Sadrita404/Split-Keyboard/IMAGES/6.png

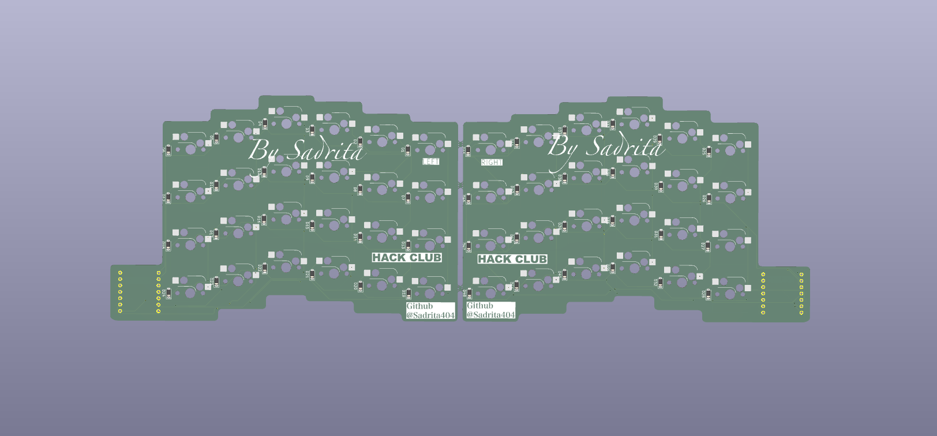
IMAGES/6.png
