Sadrita404/Split-Keyboard/IMAGES/1.png

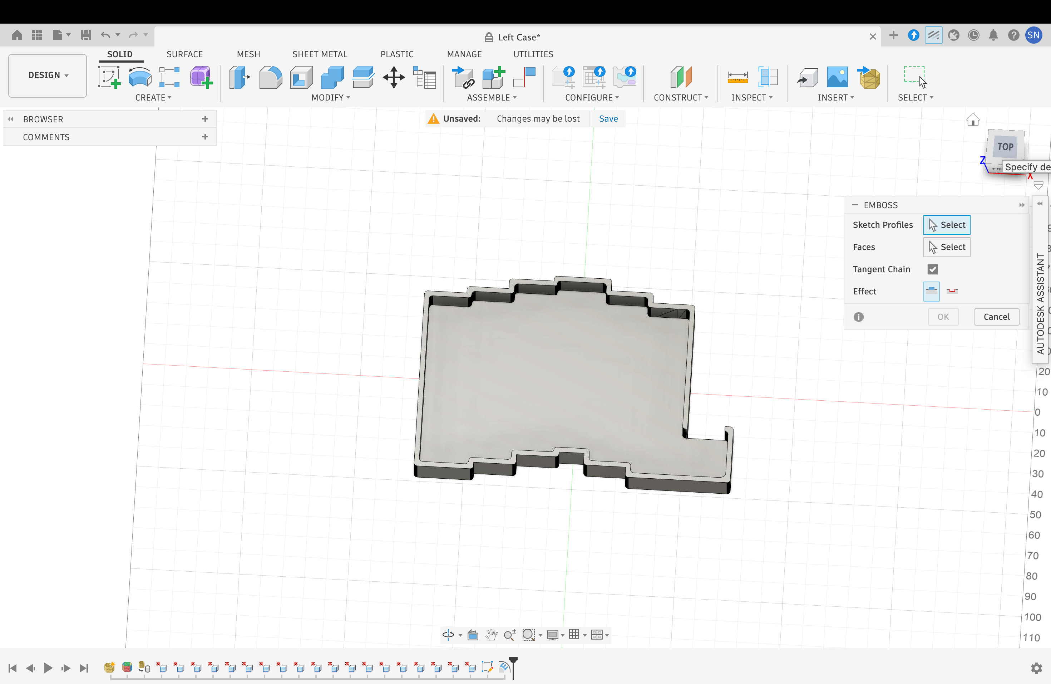
IMAGES/1.png
