Sadrita404/Split-Keyboard/IMAGES/2.png

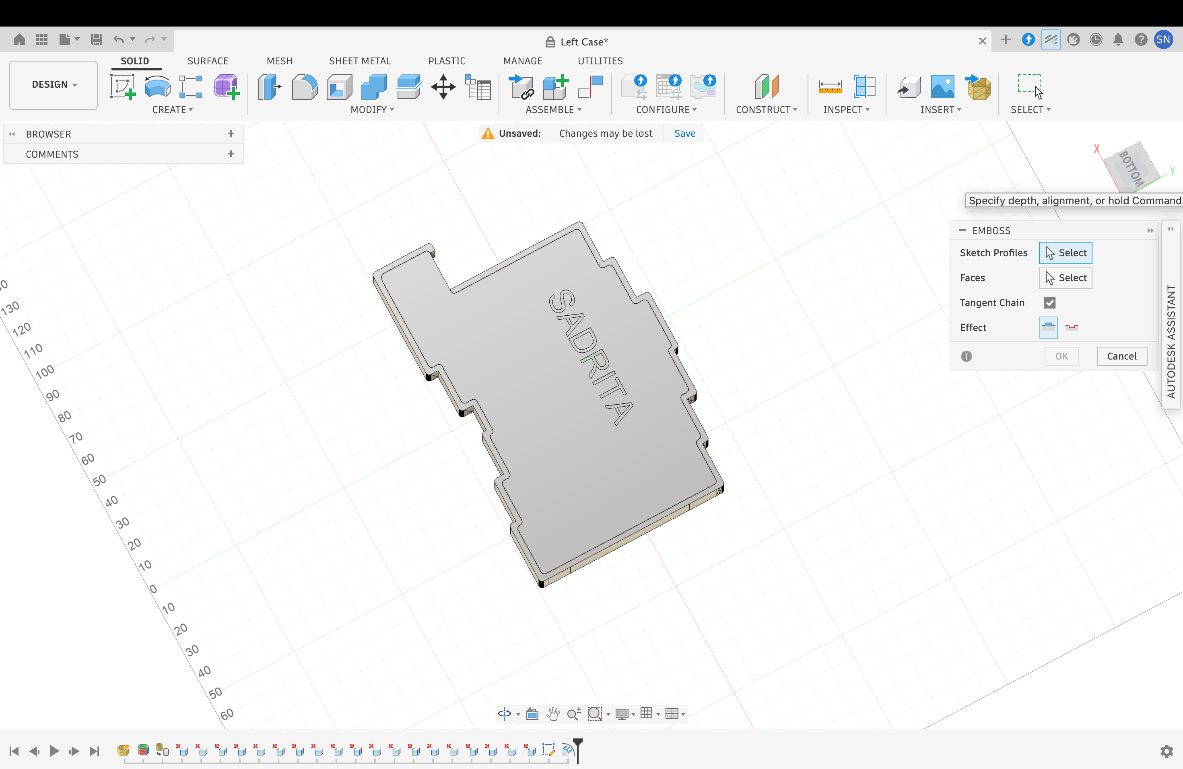
IMAGES/2.png
