Sadrita404/Split-Keyboard/IMAGES/3.png

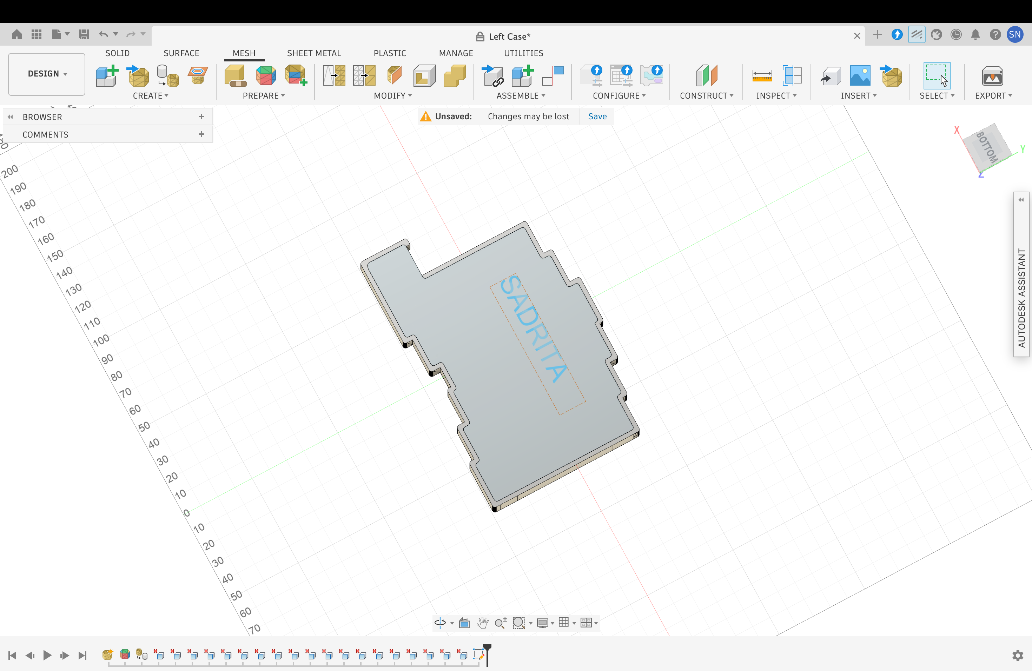
IMAGES/3.png
