Sadrita404/Split-Keyboard/IMAGES/4.png

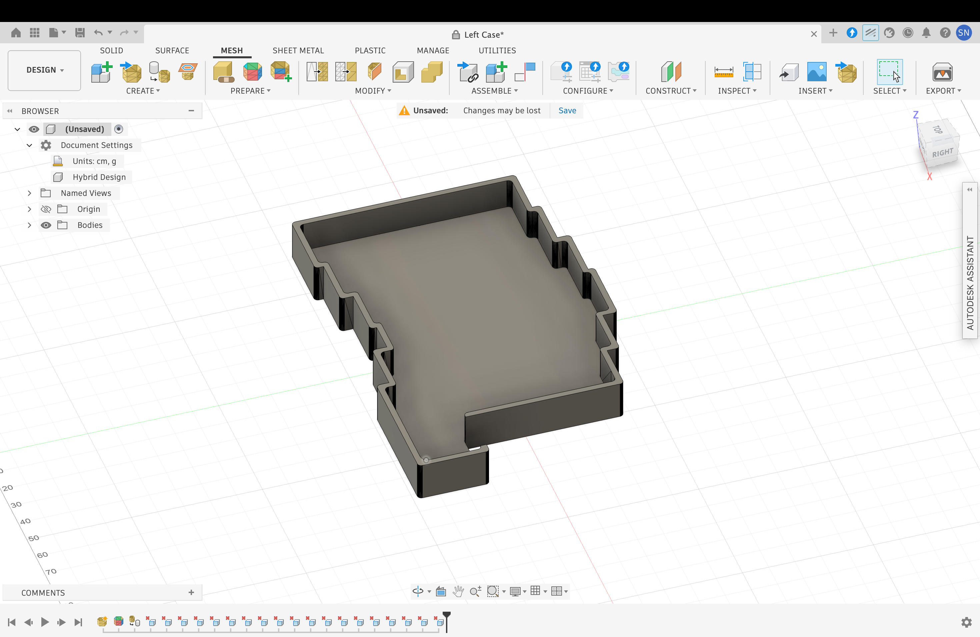
IMAGES/4.png
