Sadrita404/Split-Keyboard/IMAGES/5.png

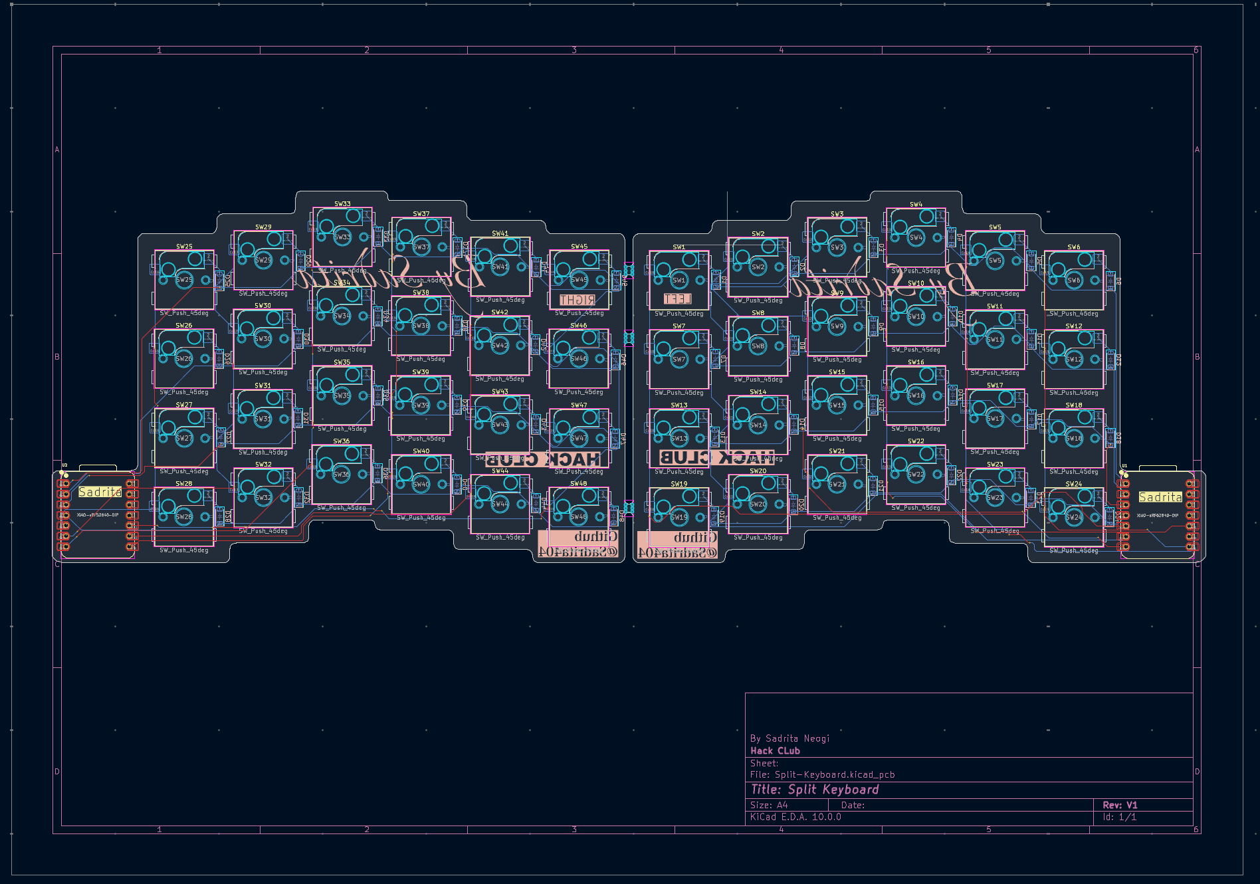
IMAGES/5.png
