Sadrita404/Split-Keyboard/IMAGES/7.png

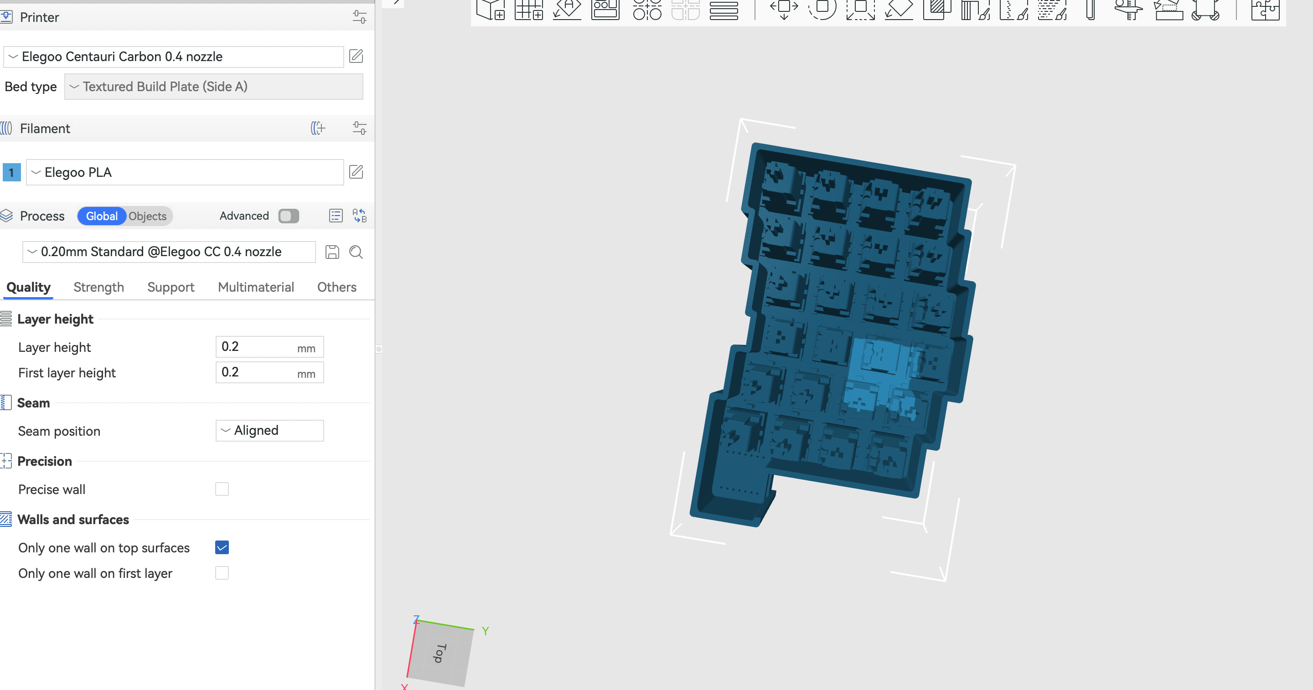
IMAGES/7.png
