Sadrita404/Split-Keyboard/IMAGES/8.png

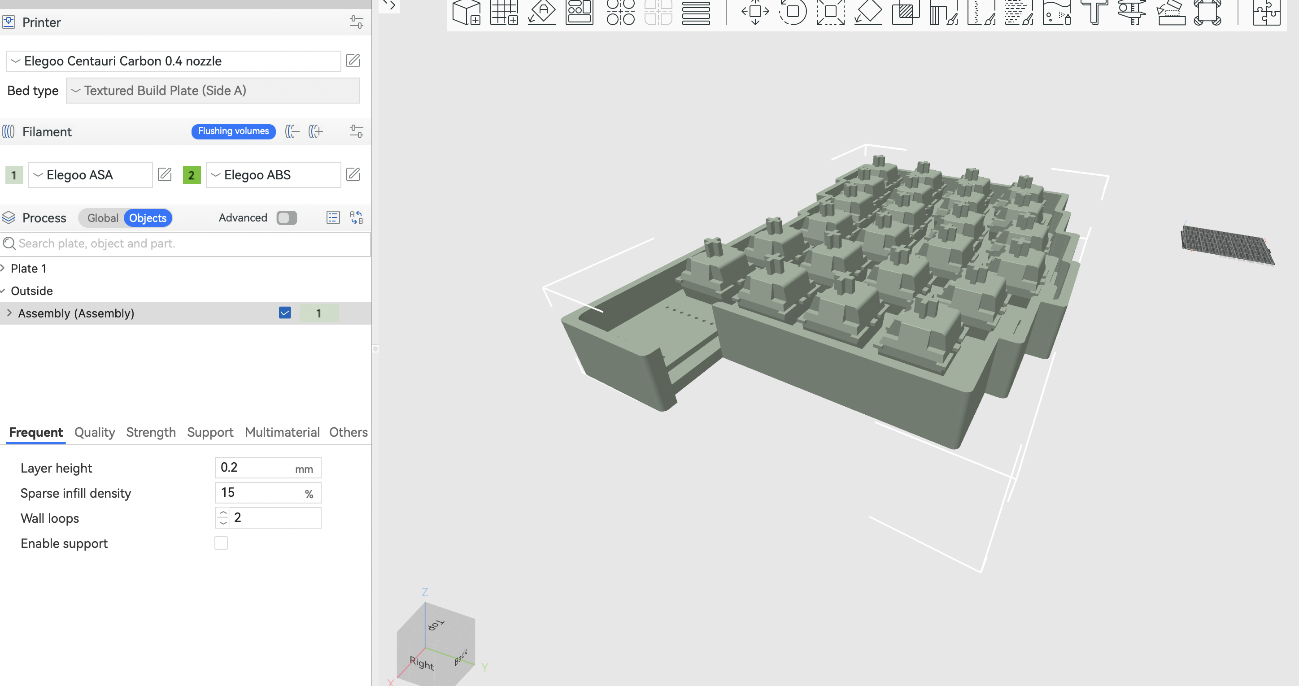
IMAGES/8.png
