Sadrita404/Split-Keyboard/IMAGES/Bill 2.png

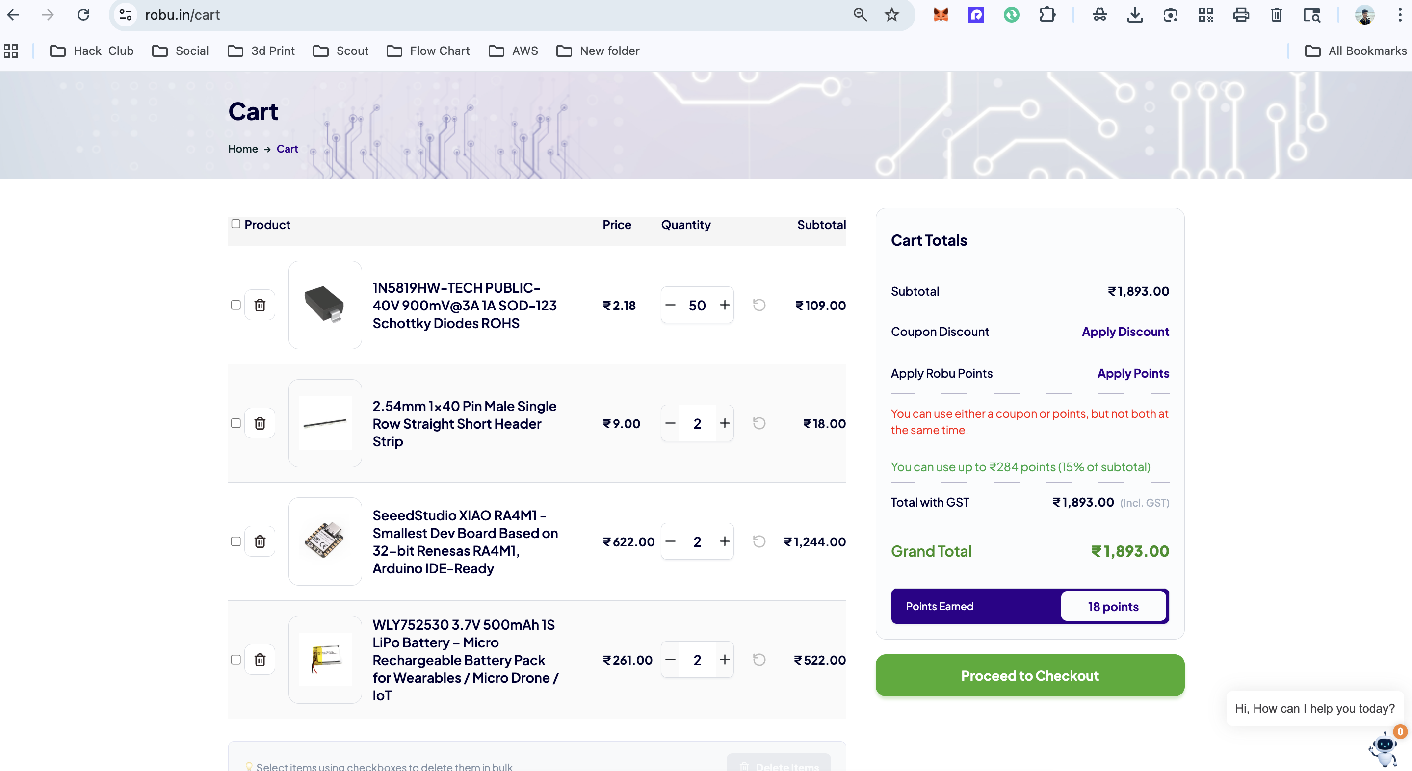
IMAGES/Bill 2.png
