Sadrita404/Split-Keyboard/IMAGES/Bill 3.png

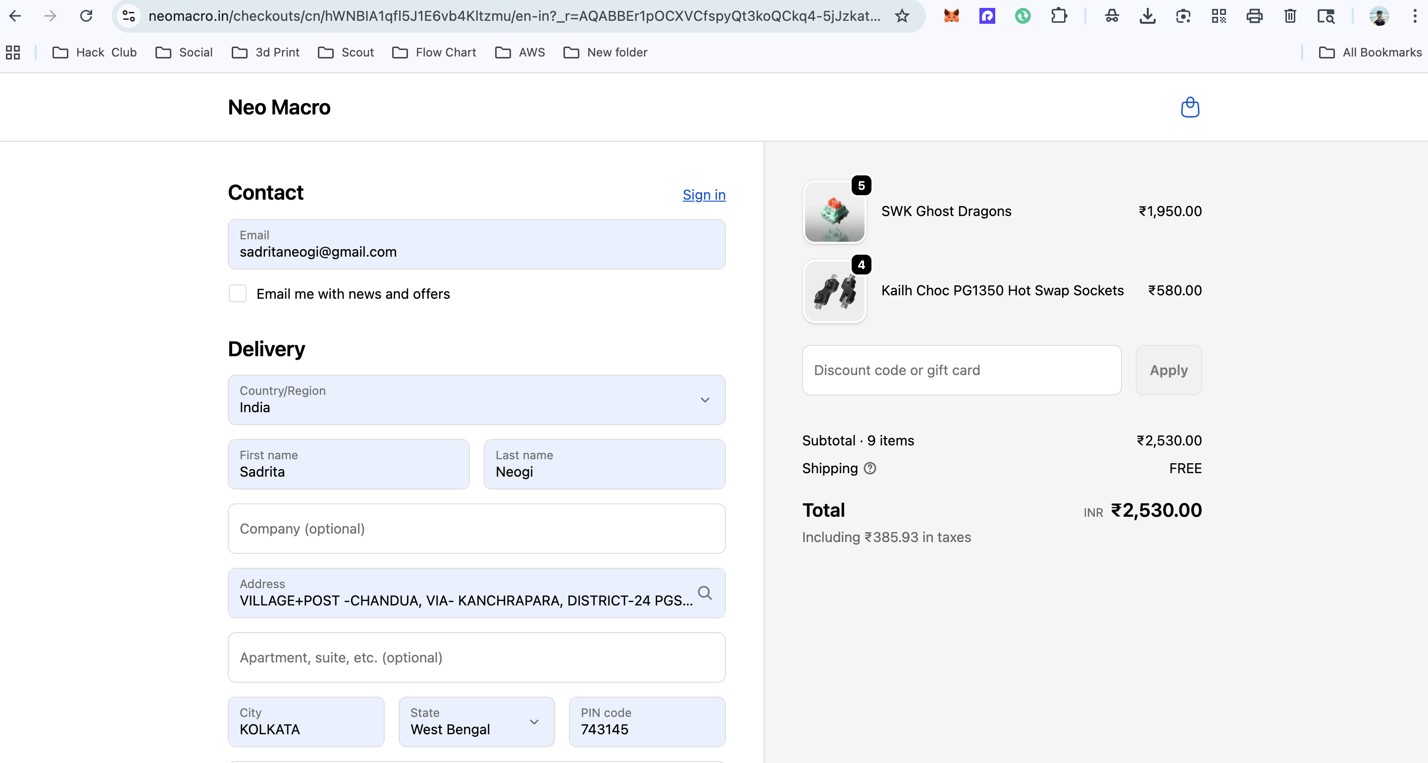
IMAGES/Bill 3.png
