Sadrita404/Split-Keyboard/IMAGES/Right sch.png

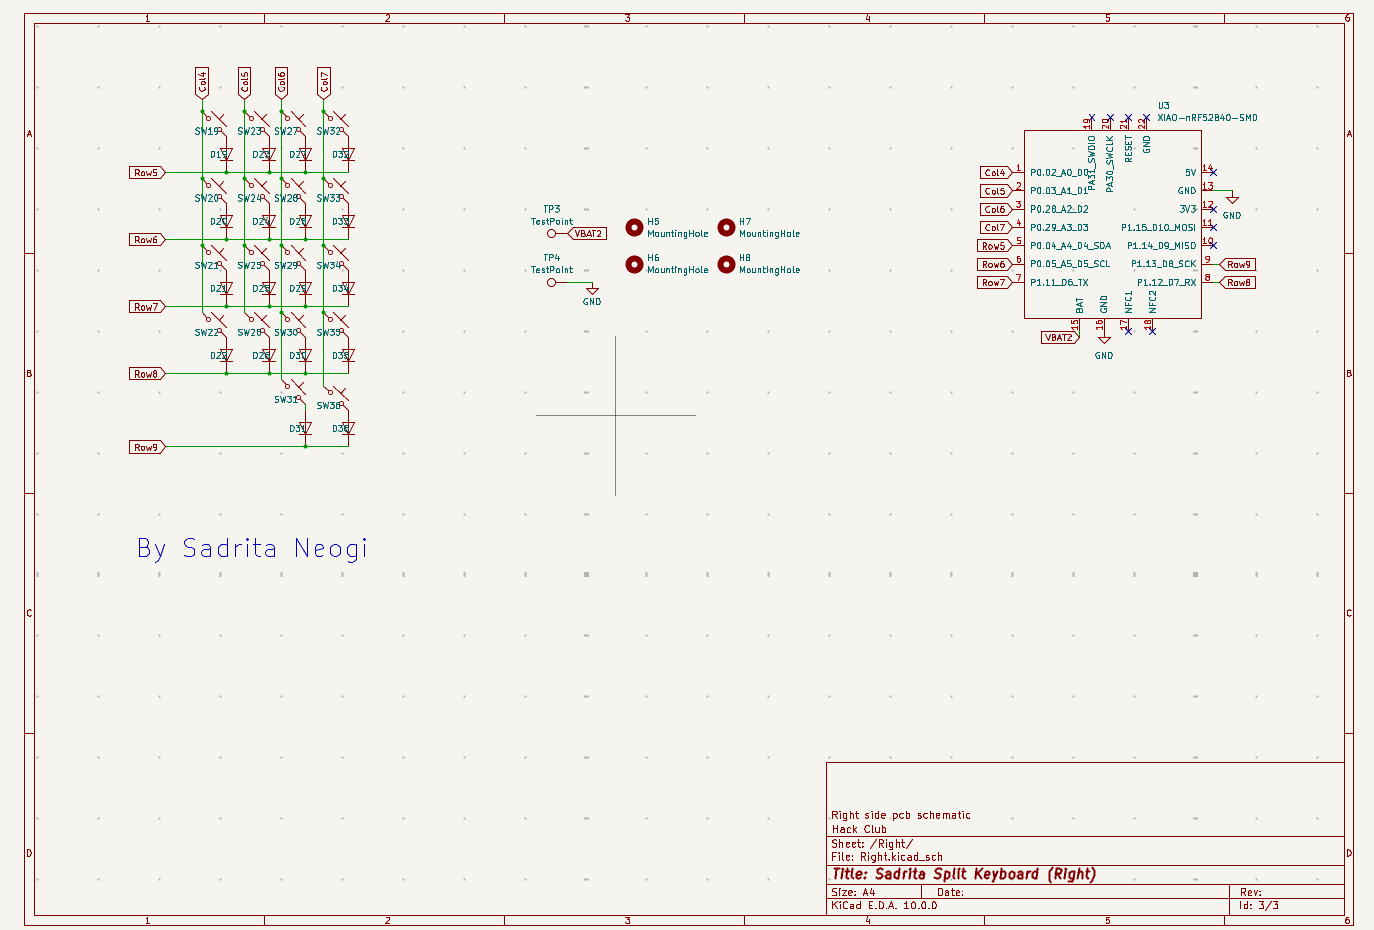
IMAGES/Right sch.png
