Sadrita404/Split-Keyboard/IMAGES/Split Keyboard (2).png

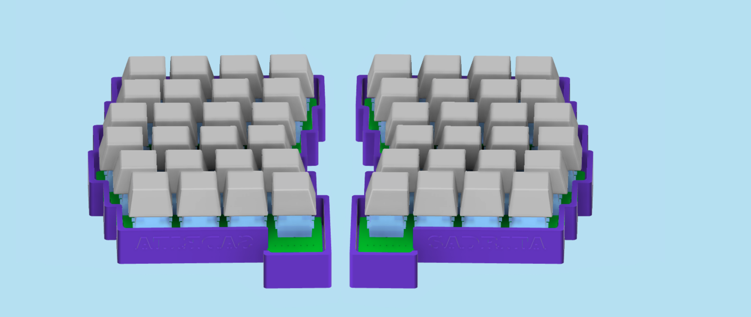
IMAGES/Split Keyboard (2).png
