Sadrita404/Split-Keyboard/IMAGES/Split Keyboard.png

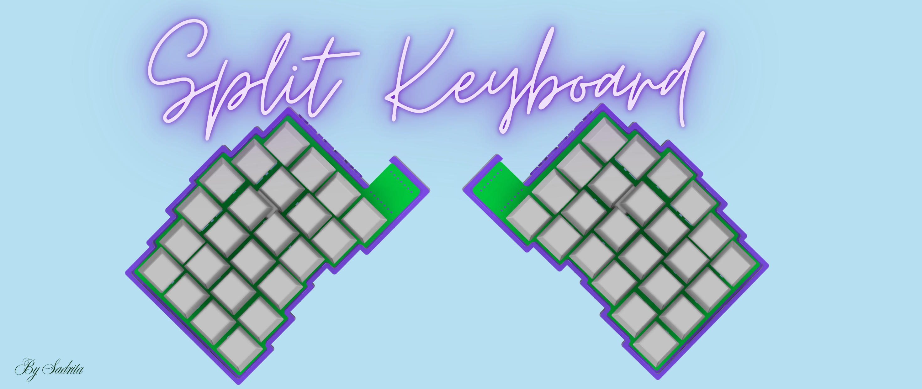
IMAGES/Split Keyboard.png
